advenacodex/ericofon-stream/docs/images/IMG_1142.jpeg

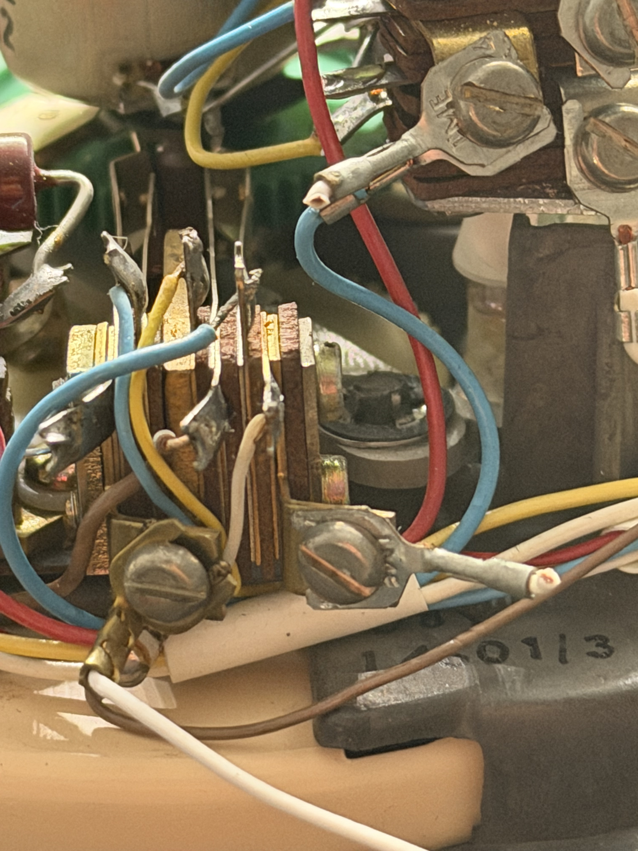
docs/images/IMG_1142.jpeg
