advenacodex/ericofon-stream/docs/images/IMG_1147.jpeg

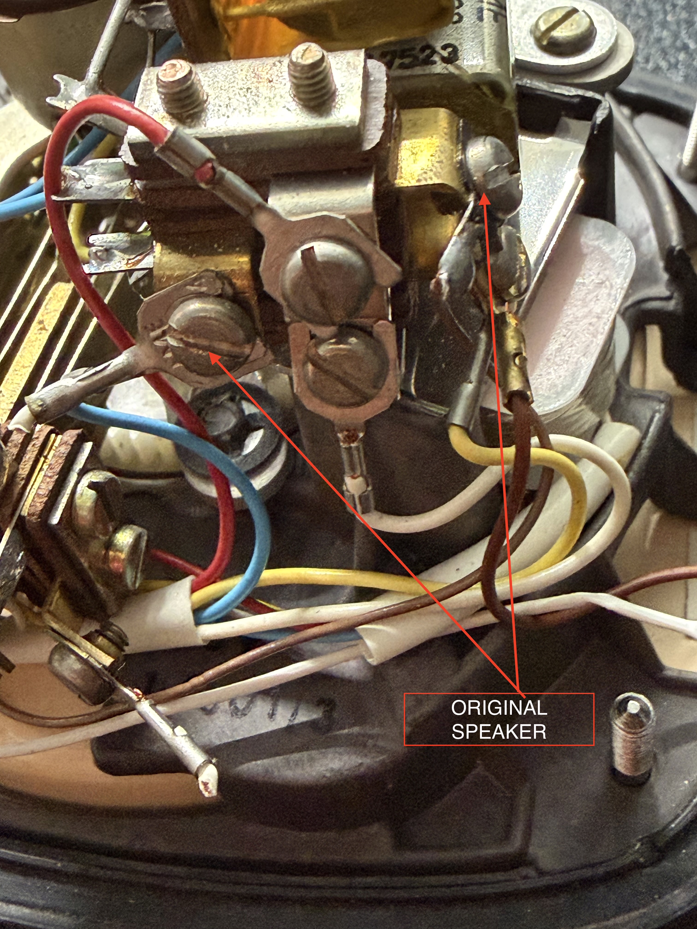
docs/images/IMG_1147.jpeg
