advenacodex/ericofon-stream/include/secrets.example.h

#ifndef SECRETS_H
#define SECRETS_H

// Configuración WiFi
const char* WIFI_SSID = "YOUR_WIFI_SSID";
const char* WIFI_PASSWORD = "YOUR_WIFI_PASSWORD";

// Configuración Navidrome
// URL del servidor (formato: http://IP:PUERTO o http://dominio.com:4533)
const char* NAVIDROME_URL = "http://192.168.1.100:4533";
const char* NAVIDROME_USER = "your_username";
const char* NAVIDROME_PASS = "your_password";

#endif
