advenacodex/ericofon-stream/test/01.test_min.cpp

// ==========================
// TEST MINIMAL - Buzzer
// ==========================


#include <driver/i2s.h>
#include <math.h>

#define I2S_BCLK 26
#define I2S_LRC  25
#define I2S_DOUT 22

#define SAMPLE_RATE 44100
#define TONE_FREQ   440.0
#ifndef PI
#define PI 3.14159265358979323846
#endif


void setup() {
  i2s_config_t i2s_config = {
    .mode = (i2s_mode_t)(I2S_MODE_MASTER | I2S_MODE_TX),
    .sample_rate = SAMPLE_RATE,
    .bits_per_sample = I2S_BITS_PER_SAMPLE_16BIT,
    .channel_format = I2S_CHANNEL_FMT_RIGHT_LEFT,
    .communication_format = I2S_COMM_FORMAT_I2S,
    .intr_alloc_flags = ESP_INTR_FLAG_LEVEL1,
    .dma_buf_count = 8,
    .dma_buf_len = 64,
    .use_apll = false,
    .tx_desc_auto_clear = true,
    .fixed_mclk = 0
  };

  i2s_pin_config_t pin_config = {
    .bck_io_num = I2S_BCLK,
    .ws_io_num = I2S_LRC,
    .data_out_num = I2S_DOUT,
    .data_in_num = I2S_PIN_NO_CHANGE
  };

  i2s_driver_install(I2S_NUM_0, &i2s_config, 0, NULL);
  i2s_set_pin(I2S_NUM_0, &pin_config);
}

void loop() {
  static float phase = 0;
  int16_t sample[2];

  float increment = 2.0 * PI * TONE_FREQ / SAMPLE_RATE;

  for (int i = 0; i < 128; i++) {
    int16_t v = (int16_t)(sin(phase) * 12000);
    sample[0] = v; // L
    sample[1] = v; // R

    size_t bytes_written;
    i2s_write(I2S_NUM_0, sample, sizeof(sample), &bytes_written, portMAX_DELAY);

    phase += increment;
    if (phase > 2 * PI) phase -= 2 * PI;
  }
}
