advenacodex/ericofon-stream/docs/images/IMG_1143.jpeg

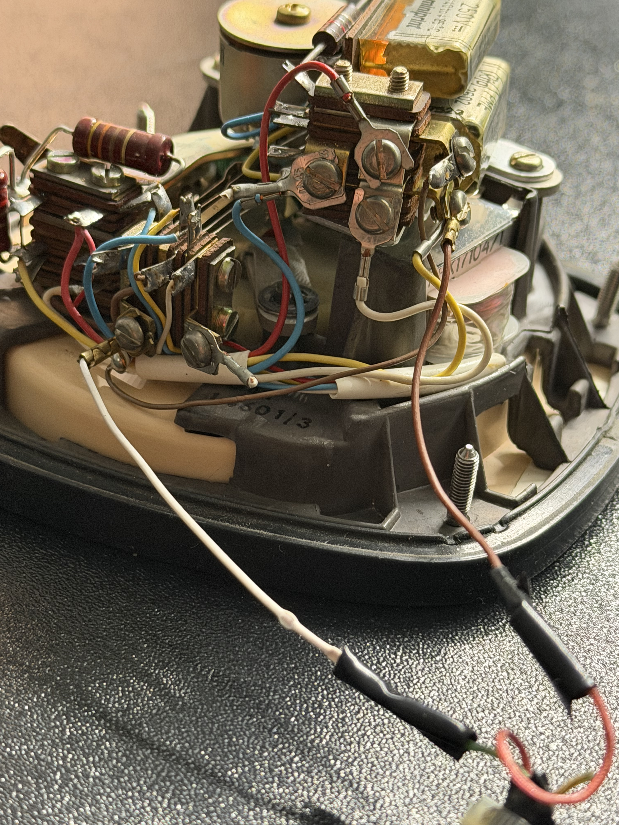
docs/images/IMG_1143.jpeg
