advenacodex/ericofon-stream/docs/images/IMG_1144.jpeg

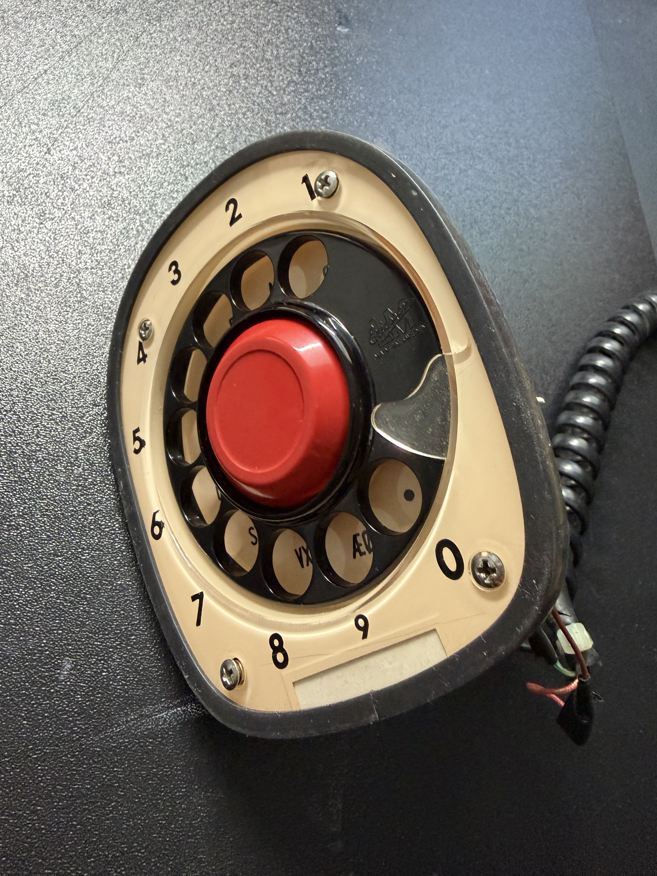
docs/images/IMG_1144.jpeg
