advenacodex/ericofon-stream/docs/images/IMG_1145.jpeg

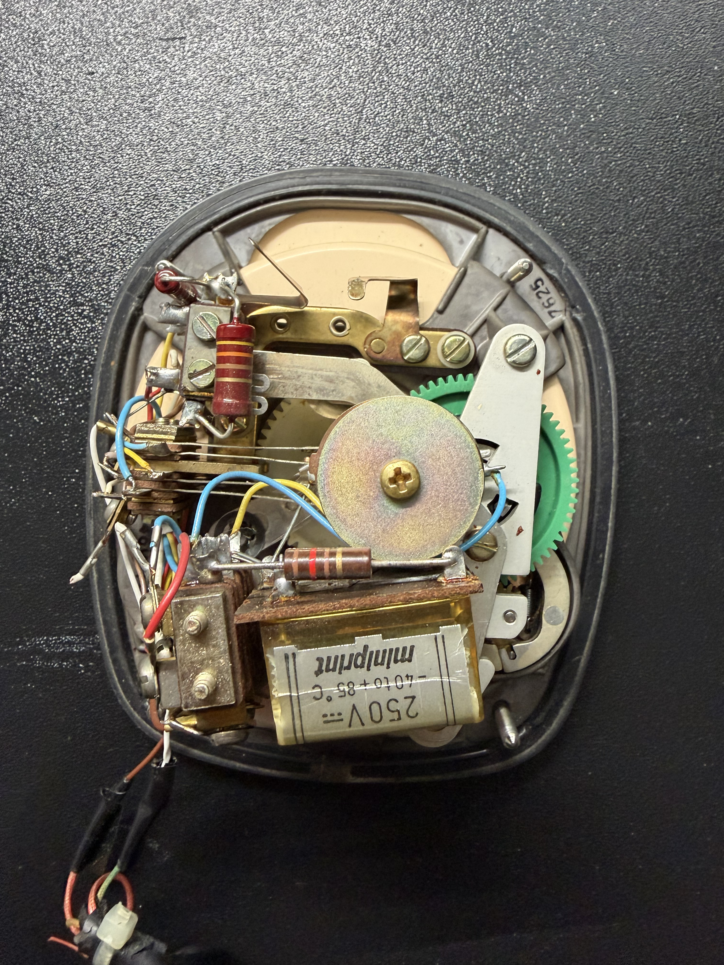
docs/images/IMG_1145.jpeg
