advenacodex/ericofon-stream/docs/images/IMG_1146.jpeg

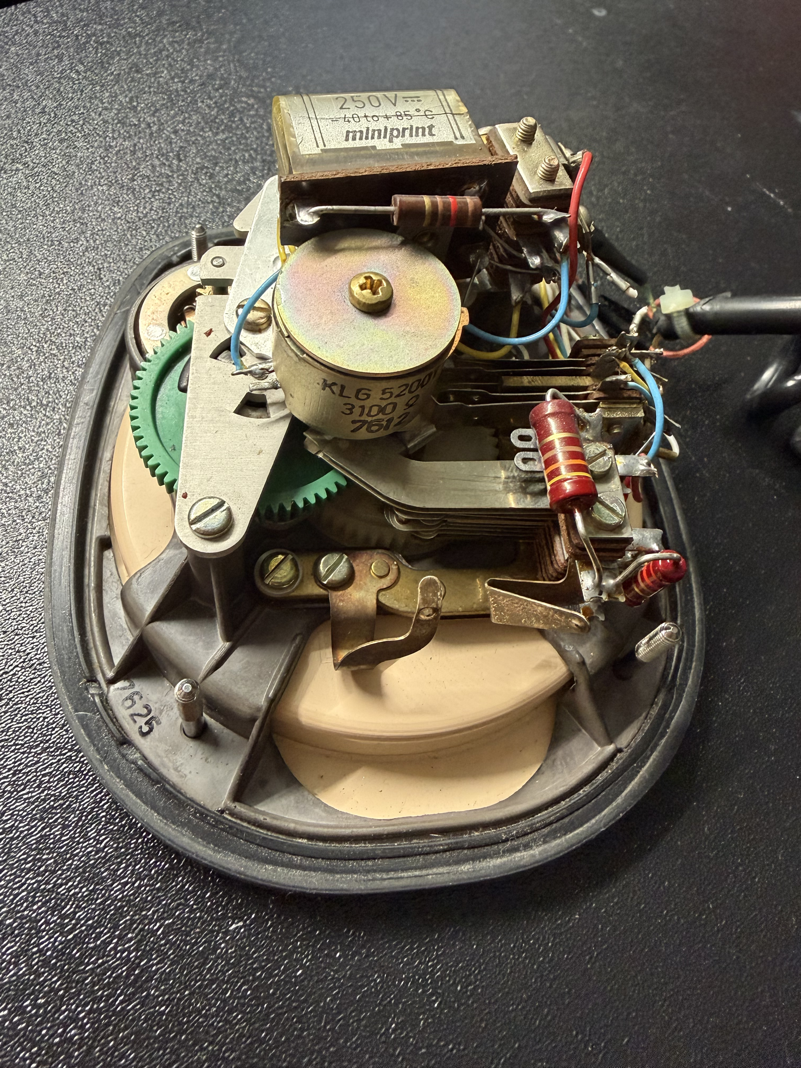
docs/images/IMG_1146.jpeg
